dwillmore/CH32V003boards/CH32V003A4M6 V4/a4m6_front_3d.png

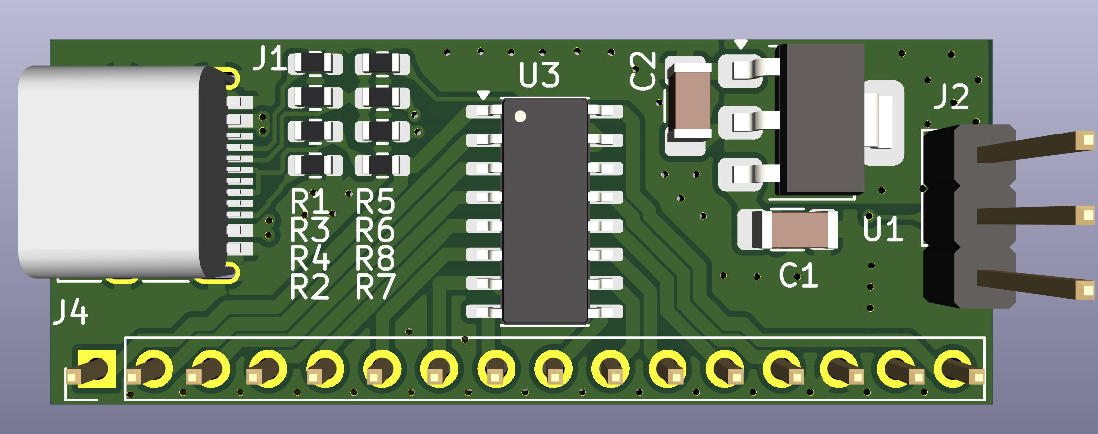
CH32V003A4M6 V4/a4m6_front_3d.png
