dwillmore/CH32V003boards/CH32V003F4P6 V4/f4p6_front_3d.png

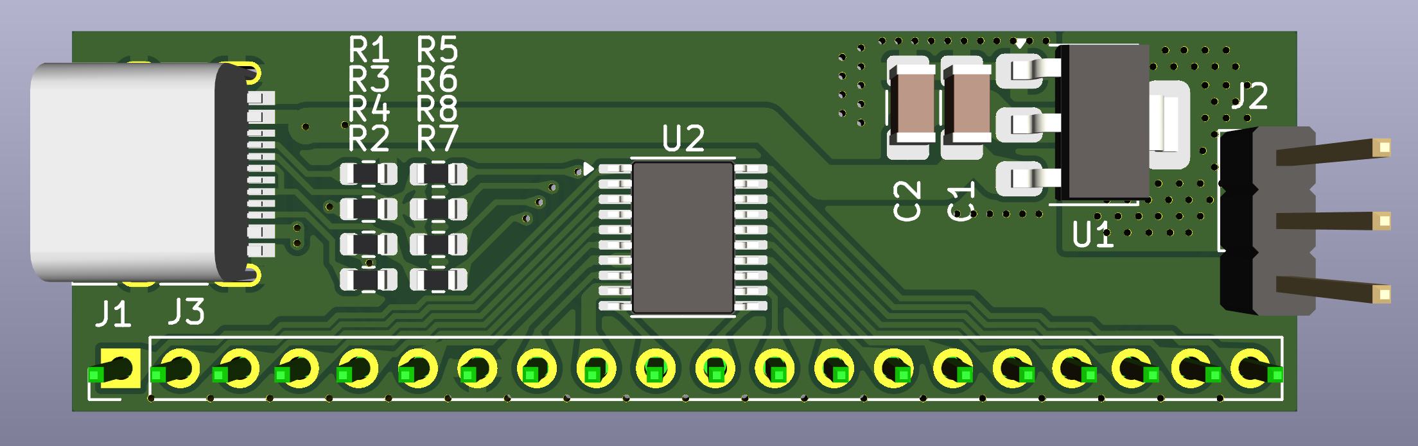
CH32V003F4P6 V4/f4p6_front_3d.png
