dwillmore/CH32V003boards/CH32V003F4U6 V4/f4u6_front.png

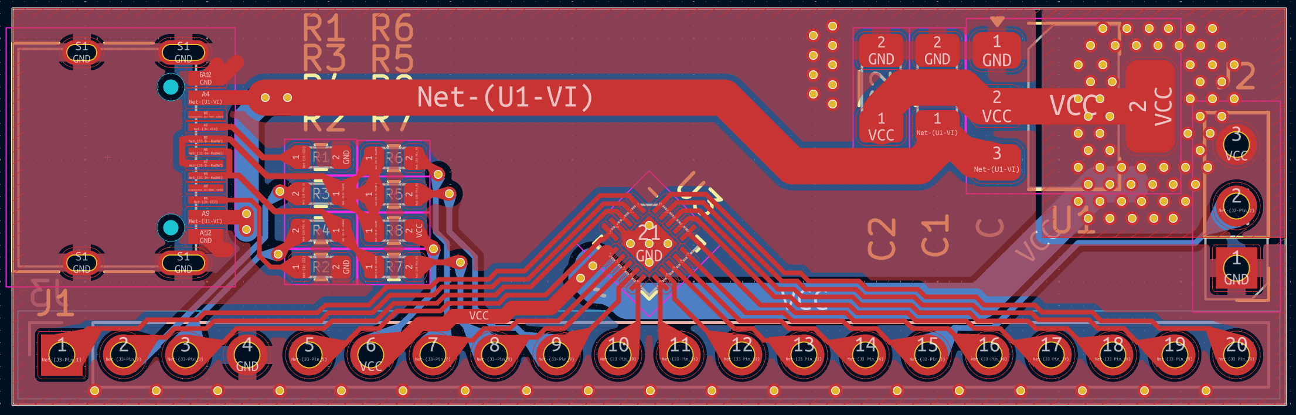
CH32V003F4U6 V4/f4u6_front.png
