dwillmore/CH32V003boards/CH32V003J4M6 V4/j4m6_front.png

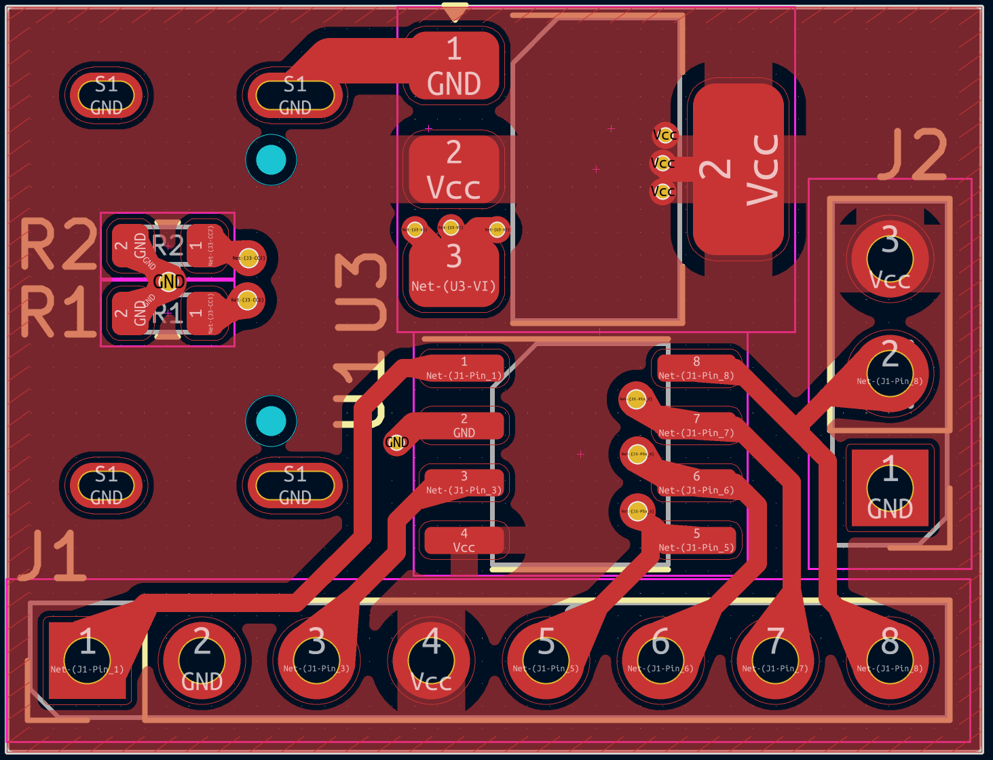
CH32V003J4M6 V4/j4m6_front.png
