dwillmore/CH32V003boards/CH32V003J4M6 V4/j4m6_front_3d.png

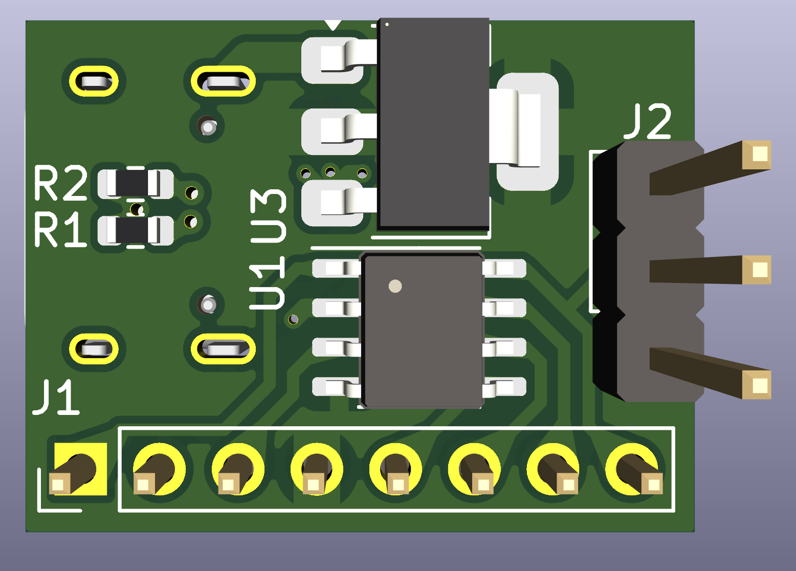
CH32V003J4M6 V4/j4m6_front_3d.png
